Ha22yX/DayVault/firmware/src/TransferBuffer.cpp

#include "TransferBuffer.h"

static uint8_t g_transfer_workspace[TRANSFER_BUFFER_COUNT * TRANSFER_BUFFER_BYTES]
    __attribute__((section(".ram2"), aligned(32)));

static_assert(sizeof(g_transfer_workspace) == 32u * 1024u,
              "transfer workspace must exactly fill SRAM2");

uint8_t* transfer_buffer(size_t index)
{
    if (index >= TRANSFER_BUFFER_COUNT) return nullptr;
    return g_transfer_workspace + index * TRANSFER_BUFFER_BYTES;
}

size_t transfer_buffer_size(void)
{
    return TRANSFER_BUFFER_BYTES;
}

uint8_t* transfer_workspace(void)
{
    return g_transfer_workspace;
}

size_t transfer_workspace_size(void)
{
    return sizeof(g_transfer_workspace);
}
