Ha22yX/DayVault/tools/dayvault_sync/dayvault/lang.py

"""Lightweight i18n (English default, Chinese) for the DayVault sync tool."""

TRANSLATIONS: dict[str, dict[str, str]] = {
    "en": {
        "title": "DayVault Sync",
        "device": "Device:",
        "sync_btn": "Sync now",
        "battery_unknown": "Battery: --",
        "battery_status": "{}% · {:.2f} V",
        "battery_charging": "{}% · {:.2f} V · Charging",
        "col_name": "Name",
        "col_size": "Size",
        "col_time": "Start time",
        "col_duration": "Duration",
        "col_status": "Status",
        "folder": "Sync folder:",
        "choose_folder": "Choose...",
        "waiting": "Waiting for device...",
        "device_detected": "Device {} connected, syncing...",
        "device_disconnected": "Device {} disconnected",
        "status_downloaded": "Downloaded",
        "status_not_downloaded": "Not downloaded",
        "status_downloading": "Downloading {}%",
        "status_failed": "Download failed",
        "sync_finished": "{} sync complete",
        "new_downloads": "new downloads {}",
        "failures": "failed {}",
        "sync_error": "{} sync error: {}",
        "no_device": "No device selected",
        "device_idle": "Device idle",
        "manual_sync": "Manual sync {}...",
        "choose_folder_title": "Choose sync folder",
        "folder_changed": "Sync folder changed to {}",
        "lang_label": "Language:",
        "lang_en": "English",
        "lang_zh": "Chinese",
        "tray_tip": "DayVault Sync",
        "tray_show": "Show window",
        "tray_quit": "Quit",
        "tray_hide": "Minimized to the system tray; click the tray icon to reopen.",
        "action_open": "Open",
        "action_delete": "Delete",
        "action_open_folder": "Open folder",
        "action_save_as": "Save as...",
        "file_unavailable_title": "File unavailable",
        "file_unavailable": "{} has not been downloaded yet.",
        "file_open_failed_title": "Open failed",
        "file_open_failed": "Could not open {}.",
        "folder_open_failed": "Could not open folder {}.",
        "save_as_title": "Save recording as",
        "audio_file_filter": "Audio files (*.opus *.wav);;All files (*)",
        "save_as_failed_title": "Save as failed",
        "save_as_failed": "Could not copy the recording: {}",
        "save_as_complete": "Saved a copy to {}",
        "delete_confirm_title": "Delete recording",
        "delete_confirm": "Delete {} from both this computer and the DayVault device?\n\nThis cannot be undone.",
        "delete_failed_title": "Delete failed",
        "delete_failed": "Could not delete {}: {}",
        "delete_partial_title": "Device file deleted",
        "delete_partial": "{} was deleted from the device, but the local copy could not be removed: {}",
        "delete_complete": "Deleted {} from the computer and device",
        "deleting_file": "Deleting {}...",
        "device_unavailable": "The DayVault device is unavailable.",
    },
    "zh": {
        "title": "DayVault \u540c\u6b65",
        "device": "\u8bbe\u5907\uff1a",
        "sync_btn": "\u7acb\u5373\u540c\u6b65",
        "battery_unknown": "\u7535\u91cf\uff1a--",
        "battery_status": "{}% \u00b7 {:.2f} V",
        "battery_charging": "{}% \u00b7 {:.2f} V \u00b7 \u5145\u7535\u4e2d",
        "col_name": "\u6587\u4ef6\u540d",
        "col_size": "\u5927\u5c0f",
        "col_time": "\u5f00\u59cb\u65f6\u95f4",
        "col_duration": "\u5f55\u5236\u65f6\u957f",
        "col_status": "\u72b6\u6001",
        "folder": "\u540c\u6b65\u6587\u4ef6\u5939\uff1a",
        "choose_folder": "\u9009\u62e9...",
        "waiting": "\u7b49\u5f85\u8bbe\u5907...",
        "device_detected": "\u68c0\u6d4b\u5230\u8bbe\u5907 {}\uff0c\u6b63\u5728\u540c\u6b65...",
        "device_disconnected": "\u8bbe\u5907\u5df2\u65ad\u5f00 {}",
        "status_downloaded": "\u5df2\u4e0b\u8f7d",
        "status_not_downloaded": "\u672a\u4e0b\u8f7d",
        "status_downloading": "\u4e0b\u8f7d\u4e2d {}%",
        "status_failed": "\u4e0b\u8f7d\u5931\u8d25",
        "sync_finished": "{} \u540c\u6b65\u5b8c\u6210",
        "new_downloads": "\u65b0\u4e0b\u8f7d {} \u4e2a",
        "failures": "\u5931\u8d25 {} \u4e2a",
        "sync_error": "{} \u540c\u6b65\u9519\u8bef\uff1a{}",
        "no_device": "\u6ca1\u6709\u9009\u4e2d\u7684\u8bbe\u5907",
        "device_idle": "\u8bbe\u5907\u7a7a\u95f2",
        "manual_sync": "\u624b\u52a8\u540c\u6b65 {}...",
        "choose_folder_title": "\u9009\u62e9\u540c\u6b65\u6587\u4ef6\u5939",
        "folder_changed": "\u540c\u6b65\u6587\u4ef6\u5939\u5df2\u66f4\u6539\u4e3a {}",
        "lang_label": "\u8bed\u8a00\uff1a",
        "lang_en": "\u82f1\u6587",
        "lang_zh": "\u4e2d\u6587",
        "tray_tip": "DayVault \u540c\u6b65",
        "tray_show": "\u6253\u5f00\u4e3b\u754c\u9762",
        "tray_quit": "\u9000\u51fa",
        "tray_hide": "\u5df2\u6700\u5c0f\u5316\u5230\u7cfb\u7edf\u6258\u76d8\uff0c\u70b9\u51fb\u6258\u76d8\u56fe\u6807\u53ef\u91cd\u65b0\u6253\u5f00\u3002",
        "action_open": "\u6253\u5f00",
        "action_delete": "\u5220\u9664",
        "action_open_folder": "\u6253\u5f00\u6240\u5728\u6587\u4ef6\u5939",
        "action_save_as": "\u53e6\u5b58\u4e3a...",
        "file_unavailable_title": "\u6587\u4ef6\u4e0d\u53ef\u7528",
        "file_unavailable": "{} \u5c1a\u672a\u4e0b\u8f7d\u5230\u7535\u8111\u3002",
        "file_open_failed_title": "\u6253\u5f00\u5931\u8d25",
        "file_open_failed": "\u65e0\u6cd5\u6253\u5f00 {}\u3002",
        "folder_open_failed": "\u65e0\u6cd5\u6253\u5f00\u6587\u4ef6\u5939 {}\u3002",
        "save_as_title": "\u5f55\u97f3\u53e6\u5b58\u4e3a",
        "audio_file_filter": "\u97f3\u9891\u6587\u4ef6 (*.opus *.wav);;\u6240\u6709\u6587\u4ef6 (*)",
        "save_as_failed_title": "\u53e6\u5b58\u4e3a\u5931\u8d25",
        "save_as_failed": "\u65e0\u6cd5\u590d\u5236\u5f55\u97f3\uff1a{}",
        "save_as_complete": "\u5df2\u5c06\u526f\u672c\u4fdd\u5b58\u5230 {}",
        "delete_confirm_title": "\u5220\u9664\u5f55\u97f3",
        "delete_confirm": "\u786e\u5b9a\u8981\u540c\u65f6\u5220\u9664\u7535\u8111\u548c DayVault \u8bbe\u5907\u4e0a\u7684 {} \u5417\uff1f\n\n\u6b64\u64cd\u4f5c\u65e0\u6cd5\u64a4\u9500\u3002",
        "delete_failed_title": "\u5220\u9664\u5931\u8d25",
        "delete_failed": "\u65e0\u6cd5\u5220\u9664 {}\uff1a{}",
        "delete_partial_title": "\u8bbe\u5907\u6587\u4ef6\u5df2\u5220\u9664",
        "delete_partial": "\u5df2\u5220\u9664\u8bbe\u5907\u4e0a\u7684 {}\uff0c\u4f46\u672c\u5730\u526f\u672c\u5220\u9664\u5931\u8d25\uff1a{}",
        "delete_complete": "\u5df2\u4ece\u7535\u8111\u548c\u8bbe\u5907\u5220\u9664 {}",
        "deleting_file": "\u6b63\u5728\u5220\u9664 {}...",
        "device_unavailable": "DayVault \u8bbe\u5907\u5f53\u524d\u4e0d\u53ef\u7528\u3002",
    },
}


class Lang:
    def __init__(self, lang: str = "en"):
        self.lang = lang if lang in TRANSLATIONS else "en"

    def tr(self, key: str, *args) -> str:
        table = TRANSLATIONS.get(self.lang, TRANSLATIONS["en"])
        value = table.get(key, key)
        if args:
            try:
                return value.format(*args)
            except Exception:
                return value
        return value
